cookie99999/6502/filesystem.asm

  .A8
  .I8

  .export cf_busy_wait
  .export cf_drq_wait
  .export cf_read_sector
  .export fat_read_params
  .export print_dir
  .export pr_current_dir
  .export fat_load_file
  
  UTC_OFFS = <-5

  ; ---------------------
  ; CompactFlash routines
  ; ---------------------

cf_busy_wait:
  lda CF_STAT
  and #CF_STAT_BSY
  bne cf_busy_wait
  rts

cf_drq_wait:
  lda CF_STAT
  and #CF_STAT_DRQ
  beq cf_drq_wait
  rts

cf_read_sector:	; 32 bit sector number, buffer ptr, count
  .A8
  .I8
  @count = 9
  @buf = 7
  @lba = 3 ; lo-lo, lo-hi, hi-lo, hi-hi
  ; todo probably want to save all the registers i clobber
  lda @lba+3, s
  ora #$e0 ; mask in other part of head reg
  sta CF_LBA_27_24
  lda @lba+2, s
  sta CF_LBA_23_16
  lda @lba+1, s
  sta CF_LBA_15_8
  lda @lba, s
  sta CF_LBA_7_0
  lda @count, s
  tax ; x = sector count
  sta CF_SEC_COUNT
  lda #CF_READ_SEC
  sta CF_CMD
  jsr cf_drq_wait

  stx workwl
  stz workwh
  ACC_16
  lda #512
  sta workw2
  jsr mul_16
  ACC_8
  IND_16
  ldy #$0000
@read_loop:
  lda CF_DATA
  sta (@buf, s), y
  iny
  cpy workw
  bne @read_loop
  ; stack cleanup
  ACC_16
  tsc
  clc
  adc #2 ; source end: 2nd byte of return address
  tax
  adc #7
  tay ; dest: top of stack frame
  lda #1 ; copying 2 bytes (just rts address)
  mvp #0, #0 ; mvp stops when c is below zero, so c must be size-1
  tya
  tcs
  ACC_8
  IND_8
  rts

  ; ---------------
  ; FAT16 utilities
  ; ---------------

cluster_to_sector: ; cluster in c, sector returned in workw+workw2
  .A16
  .I8
  sec
  sbc #2
  sta workw
  lda sec_per_cluster
  and #$00ff
  sta workw2
  jsr mul_16
  clc
  lda data_start
  adc workw
  sta workw
  lda data_start+2
  adc workw2
  sta workw2
  rts

fat_read_params: ; vbr should be in secbuf
  .A8
  IND_16
  ; fat start sector
  ldx #FAT_BPB_RES_SECTORS
  lda sec_buf, x
  clc
  adc vol_start
  sta fat_start
  lda sec_buf+1, x
  adc vol_start+1
  sta fat_start+1
  lda #0 ; res sectors is only 2 bytes
  adc vol_start+2
  sta fat_start+2
  lda #0
  adc vol_start+3
  sta fat_start+3
  IND_8

  ; root start sector
  ACC_16
  lda sec_buf + FAT_BPB_NUM_FATS
  and #$00ff ; only one byte
  sta workw
  lda sec_buf + FAT_BPB_SECTORS_PER_FAT
  sta workw2
  jsr mul_16
  clc
  lda fat_start
  adc workw
  sta root_start
  lda fat_start+2
  adc workw2
  sta root_start+2 ; root_start = fat_start + (num_fats * sec_per_fat)

  ; data region start sector
  lda sec_buf + FAT_BPB_NUM_ROOT_ENTRIES
  sta workw
  lda #$0020 ; bytes per entry
  sta workw2
  jsr mul_16
  ; assume bytes per sector is 512 to avoid a divide, fix later
  .repeat 9
  lsr workw2
  ror workw
  .endrep
  clc
  lda root_start
  adc workw
  sta data_start
  lda root_start+2
  adc workw2
  sta data_start+2

  ACC_8
  lda sec_buf + FAT_BPB_SECTORS_PER_CLUSTER
  sta sec_per_cluster
  
  rts

fat_next_cluster: ; current cluster in c, next returned in c, carry set if last one
  ; TODO fix for >512 bytes of fat
  .A16
  IND_16
  asl ; x2
  tax
  lda fat_buf, x
  cmp #$ffff
  bne :+
  sec
  IND_8
  rts
:
  clc
  IND_8
  rts

fat_get_parent:	; directory cluster num in c, returns parent cluster in c
  .A8
  .I8
  phx
  phy
  ACC_16
  jsr fat_load_cluster
  ACC_8
  LD_PTR str_dot_dot_filename
  jsr fat_find_relative
  bcc :+
  LD_PTR str_crazy_error
  jsr puts
  sec
  :
  ply
  plx
  rts ; parent's cluster should be in c now

fat_load_cluster: ; cluster in c, first sector loaded to secbuf
  .A16
  .I8
  pha
  phy
  phx
  jsr cluster_to_sector
  ACC_8
  lda #$01
  pha
  pea sec_buf
  lda workw2h
  pha
  lda workw2l
  pha
  lda workwh
  pha
  lda workwl
  pha
  jsr cf_read_sector
  ACC_16
  plx
  ply
  pla
  rts
  
  ; TODO replace with multi-sector load
  ; at $80 sectors per cluster its obviously 64k
  ; which won't fit in low ram
fat_load_entire_cluster: ; cluster in c, buffer pointer in workw
  .A16
  .I8
  pha
  phy
  phx
  sta workw2 ; backup cluster num
  ACC_8
  lda sec_per_cluster
  pha
  ACC_16
  pei (workw)
  lda workw2
  jsr cluster_to_sector
  ACC_8
  lda workw2h
  pha
  lda workw2l
  pha
  lda workwh
  pha
  lda workwl
  pha
  jsr cf_read_sector
  ACC_16
  plx
  ply
  pla
  rts

fat_find_relative: ; returns cluster in c if found, carry set and c invalid otherwise
  ; current directory entry assumed to be in sec_buf
  ; pointer to 11 byte filename in workw
  ; return entry # * $20 in retw
  ; TODO: handle directory bigger than 512B, dedicated buffer for current dir data,
  ; search subdirectories, etc etc etc
  .A8
  .I8
  phx
  phy
  IND_16
  ldx #$0000
  ldy #$0000
@outer:
  stx workw2
  lda sec_buf+FAT_DIR_ATTR, x
  and #FAT_ATTR_VOL_ID
  bne @mismatch ; skip volume id and also lfn
@loop:
  lda sec_buf+FAT_DIR_NAME, x
  beq @bad_quit ; no more entries, no match
  cmp (workw), y
  bne @mismatch
  inx
  iny
  cpy #$000b ; 11 characters
  bne @loop
  ; all characters matched, get cluster and quit
  ldx workw2
  lda sec_buf+FAT_DIR_CLUSTER+1, x
  xba
  lda sec_buf+FAT_DIR_CLUSTER, x
  clc
  bra @quit
@mismatch: ; move to next entry and try again
  ldx workw2
  ACC_16
  txa
  clc
  adc #$0020
  tax
  ACC_8
  ldy #$0000
  bra @outer
@bad_quit:
  sec
@quit:
  stx retw
  IND_8
  ply
  plx
  rts

fat_load_file: ; pointer to name in workw, buffer in c
  .A8
  .I8
  sta scratch
  xba
  sta scratch+1
  jsr fat_find_relative
  bcc :+
  LD_PTR str_file
  jsr puts
  LD_PTR str_err_noexist
  jsr puts
  sec
  rts
:
  ; directory offset in retw, find size
  ACC_16
  IND_16
  sta scratch+2 ; save cluster num
  ldx retw
  lda sec_buf+FAT_DIR_SIZE, x
  sta workw
  lda sec_buf+FAT_DIR_SIZE+2, x
  sta workw2
  IND_8
  ; now divide by 512 to get sector count
  .repeat 9
  lsr workw2
  ror workw
  .endrep
  lda workw
  bne :+ ; if its under 512 it will need to be adjusted to 1 sector
  inc workw
:	
  cmp #$0100
  bcc :+
  ; more than 255 sectors, figure this out later
  ACC_8
  lda #'X'
  jsr putchar
  rts
  :
  ACC_8
  lda workwl
  pha
  ACC_16
  pei (scratch)
  lda scratch+2
  jsr cluster_to_sector
  ACC_8
  lda workw2h
  pha
  lda workw2l
  pha
  lda workwh
  pha
  lda workwl
  pha
  jsr cf_read_sector
  rts

  ; ------------------------
  ; File management routines
  ; ------------------------

change_dir: ; pointer to name in workw
  .A8
  .I8
  jsr fat_find_relative
  bcc :+
  LD_PTR str_dir
  jsr puts
  LD_PTR str_err_noexist
  jsr puts
  sec
  rts
:
  sta current_dir
  xba
  sta current_dir+1
  xba
  clc
  rts
  
pr_current_dir:
  .A8
  .I8
  lda #'/'
  jsr putchar
  ACC_16
  lda current_dir
  bne :+
  brl @quit
:	
  pha
  jsr fat_load_cluster
  pla
  ldx #$00
@parent_loop: ; follow .. entries until we get back to root
  pha ; push them so we can then traverse back down, printing names
  inx ; x = num levels
  ACC_8
  jsr fat_get_parent
  ACC_16
  cmp #$0000
  beq @end_loop ; parent of zero means it's just under / which we already printed
  bra @parent_loop
@end_loop: ; stack should now contain each cluster all the way down to current dir
  ; load root dir to start finding and printing names
  ACC_8
  phy
  phx
  lda #1
  pha
  pea sec_buf
  lda root_start+3
  pha
  lda root_start+2
  pha
  lda root_start+1
  pha
  lda root_start
  pha
  jsr cf_read_sector
  ACC_16
  plx
  ply
  txy ; y = total number of cluster numbers pushed
  IND_16
@name_loop:
  ldx #$0000
  pla
  pha ; need it in a but still saved
@find_entry: ; get to the entry matching the cluster
  cmp sec_buf+FAT_DIR_CLUSTER, x
  beq @found
@no_match:
  pha
  txa
  clc
  adc #$0020
  tax
  pla
  bra @find_entry
@found: ; now print the name
  lda sec_buf+FAT_DIR_NAME, x
  and #$00ff
  cmp #$e5 ; skip deleted
  beq @no_match
  lda sec_buf+FAT_DIR_ATTR, x
  and #FAT_ATTR_VOL_ID ; skip vol ids
  bne @no_match
  ACC_8
  phy
  ldy #$0000
@print_loop:
  lda sec_buf+FAT_DIR_NAME, x
  cmp #' '
  beq @done_print
  jsr putchar
  inx
  iny
  cpy #11
  bne @print_loop
@done_print:
  lda #'/'
  jsr putchar
  ACC_16
  ply
  pla
  dey
  beq @quit ; all levels popped and printed, done
  phy
  IND_8
  jsr fat_load_cluster
  IND_16
  ply
  bra @name_loop
@quit:
  ACC_8
  IND_8
  CRLF
  rts

print_dir: ; assuming root dir in sec_buf for now
  ACC_8
  IND_16
  ldx #$0000
@loop:
  lda sec_buf + FAT_DIR_NAME, x
  bne :+
  brl @quit; names never have zeroes
:
  cmp #$e5 ; deleted files start with e5
  bne :+
  brl @skip
:	
  lda sec_buf + FAT_DIR_ATTR, x
  and #%00001010 ; don't display hidden or volume name entries
  beq :+
  brl @skip
:	
  lda sec_buf + FAT_DIR_ATTR, x
  and #$10 ; directory?
  beq :+
  lda #'D'
  jsr putchar
  bra :++
:
  lda #' '
  jsr putchar
:
  lda #' '
  jsr putchar
  phx
  ACC_16
  txa
  clc
  adc #FAT_DIR_NAME
  tax
  ACC_8
  ldy #0
@nameloop:
  lda sec_buf, x
  jsr putchar
  inx
  iny
  cpy #11
  bne @nameloop
  plx
  lda #TAB
  jsr putchar
  lda sec_buf + FAT_DIR_MTIME, x
  xba
  lda sec_buf + FAT_DIR_MTIME+1, x
  xba
  phx
  IND_8
  jsr pr_fat_time
  IND_16
  plx

  lda #' '
  jsr putchar
  lda sec_buf + FAT_DIR_MTIME_DATE, x
  xba
  lda sec_buf + FAT_DIR_MTIME_DATE+1, x
  xba
  phx
  IND_8
  jsr pr_fat_date
  IND_16
  plx
  
  lda #TAB
  jsr putchar
  lda #TAB
  jsr putchar
  lda sec_buf + FAT_DIR_SIZE+3, x
  sta workqh+1
  lda sec_buf + FAT_DIR_SIZE+2, x
  sta workqh
  lda sec_buf + FAT_DIR_SIZE+1, x
  sta workql+1
  lda sec_buf + FAT_DIR_SIZE, x
  sta workql
  phx
  IND_8
  jsr pr_fat_filesize
  IND_16
  plx
  CRLF
@skip:
  ACC_16
  txa
  clc
  adc #$0020
  tax
  ACC_8
  brl @loop
@quit:
  IND_8
  rts

  ; -------------------------
  ; Display and misc routines
  ; -------------------------

pr_bcd:	; bcd byte in a, does not check validity
  .A8
  .I8
  pha
  and #$f0
  lsr
  lsr
  lsr
  lsr
  clc
  adc #$30
  jsr putchar
  pla
  and #$0f
  clc
  adc #$30
  jsr putchar
  rts

  ; credit Andrew Jacobs (http://6502.org/source/integers/hex2dec-more.htm)
bin_to_bcd_16: ; input in workw
  .A8
  .I8
  phx
  sed
  stz workw2l
  stz workw2h
  ldx #16
@loop:
  asl workwl
  rol workwh
  lda workw2l
  adc workw2l
  sta workw2l
  lda workw2h
  adc workw2h
  sta workw2h
  dex
  bne @loop

  lda workw2h
  xba
  lda workw2l
  plx
  cld
  rts

bin_to_bcd_32: ; input in workq, output in workb2+workq2
  .A8
  .I8
  phx
  sed
  stz workq2l
  stz workq2l+1
  stz workq2h
  stz workq2h+1
  stz workb2
  ldx #32
@loop:
  asl workql
  rol workql+1
  rol workqh
  rol workqh+1
  lda workq2l
  adc workq2l
  sta workq2l
  lda workq2l+1
  adc workq2l+1
  sta workq2l+1
  lda workq2h
  adc workq2h
  sta workq2h
  lda workq2h+1
  adc workq2h+1
  sta workq2h+1
  lda workb2
  adc workb2
  sta workb2
  dex
  bne @loop

  plx
  cld
  rts
  
  ; credit Lee Davison (http://6502.org/users/mycorner/6502/shorts/bin2bcd.html)
b2b_table:	
  .byte $63, $31, $15, $07, $03, $01, $00
  
bin_to_bcd: ; assumes input <= 99, result in a
  .A8
  .I8
  phx
  sed
  sta workb
  lda #$00
  ldx #$07
@bit_loop:
  lsr workb
  bcc @skip_add
  adc b2b_table - 1, x
@skip_add:
  dex
  bne @bit_loop

  plx
  cld
  rts
  
pr_fat_time: ; time in c, 15..11 H 10..5 M 4..0 S/2
  .A8
  pha
  xba
  pha
  lsr
  lsr
  lsr
  ; ignoring timezone fixing for now
  ;clc
  ;adc #UTC_OFFS ; linux stores mtimes as utc; not sure about other os
  jsr bin_to_bcd
  jsr pr_bcd
  lda #':'
  jsr putchar
  
  pla
  and #%00000111
  asl
  asl
  asl
  pha
  lda 2, s
  lsr
  lsr
  lsr
  lsr
  lsr
  ora 1, s
  jsr bin_to_bcd
  jsr pr_bcd
  lda #':'
  jsr putchar
  
  pla
  pla
  and #%00011111
  asl a ; seconds stored divided by 2
  jsr bin_to_bcd
  jsr pr_bcd
  rts

pr_fat_date: ; date in c, 15..9 y-1980, 8..5 m 4..0 d
  pha
  xba
  pha
  lsr
  ACC_16
  and #$00ff
  clc
  adc #1980
  sta workw
  ACC_8
  jsr bin_to_bcd_16
  xba
  jsr pr_bcd
  xba
  jsr pr_bcd
  lda #'-'
  jsr putchar

  pla
  and #$01
  asl
  asl
  asl
  pha
  lda 2, s
  lsr
  lsr
  lsr
  lsr
  lsr
  ora 1, s
  jsr bin_to_bcd
  jsr pr_bcd
  lda #'-'
  jsr putchar

  pla
  pla
  and #%00011111
  jsr bin_to_bcd
  jsr pr_bcd
  rts

pr_fat_filesize: ; size in workq
  ACC_16
  lda #$ffff
  sta workq2l
  lda #$000f
  sta workq2h ; over 1mb?
  lda workqh
  cmp workq2h
  bne @donemb
  lda workql
  cmp workq2l
  bne @donemb
  bra @skipmb ; == f,ffff
@donemb:
  bcc @skipmb
  brl @pr_mb
@skipmb:
  lda #$03ff
  sta workq2l
  stz workq2h ; over 1kb?
  lda workqh
  cmp workq2h
  bne @donekb
  lda workql
  cmp workq2l
  beq @pr_b ; == 3ff
@donekb:
  bcs @pr_kb
  
@pr_b:
  ACC_8
  jsr bin_to_bcd_32
  lda workb2
  jsr pr_bcd
  lda workq2h+1
  jsr pr_bcd
  lda workq2h
  jsr pr_bcd
  lda workq2l+1
  jsr pr_bcd
  lda workq2
  jsr pr_bcd
  lda #' '
  jsr putchar
  lda #'B'
  jsr putchar
  brl @quit

@pr_kb:
  ACC_16
  .repeat 10
  lsr workqh
  ror workql
  .endrep
  ACC_8
  jsr bin_to_bcd_32
  lda workb2
  jsr pr_bcd
  lda workq2h+1
  jsr pr_bcd
  lda workq2h
  jsr pr_bcd
  lda workq2l+1
  jsr pr_bcd
  lda workq2
  jsr pr_bcd
  lda #' '
  jsr putchar
  lda #'K'
  jsr putchar
  lda #'i'
  jsr putchar
  lda #'B'
  jsr putchar
  brl @quit

@pr_mb:
  ACC_16
  .repeat 20
  lsr workqh
  ror workql
  .endrep
  ACC_8
  jsr bin_to_bcd_32
  lda workb2
  jsr pr_bcd
  lda workq2h+1
  jsr pr_bcd
  lda workq2h
  jsr pr_bcd
  lda workq2l+1
  jsr pr_bcd
  lda workq2
  jsr pr_bcd
  lda #' '
  jsr putchar
  lda #'M'
  jsr putchar
  lda #'i'
  jsr putchar
  lda #'B'
  jsr putchar

@quit:
  rts

  ; -------
  ; Strings
  ; -------

str_file:
  .byte "file ", 0
str_dir:
  .byte "directory ", 0
str_err_lba:
  .byte "couldn't set lba mode", CR, LF, 0
str_err_8bit:
  .byte "couldn't set 8 bit mode", CR, LF, 0
str_err_noexist:
  .byte "does not exist", CR, LF, 0
str_crazy_error:
  .byte "somehow .. doesn't exist", CR, LF, 0
str_dot_dot_filename:
  .byte "..         "
